jankae/BigRedStopwatch/Pictures/IMG_2714.JPG

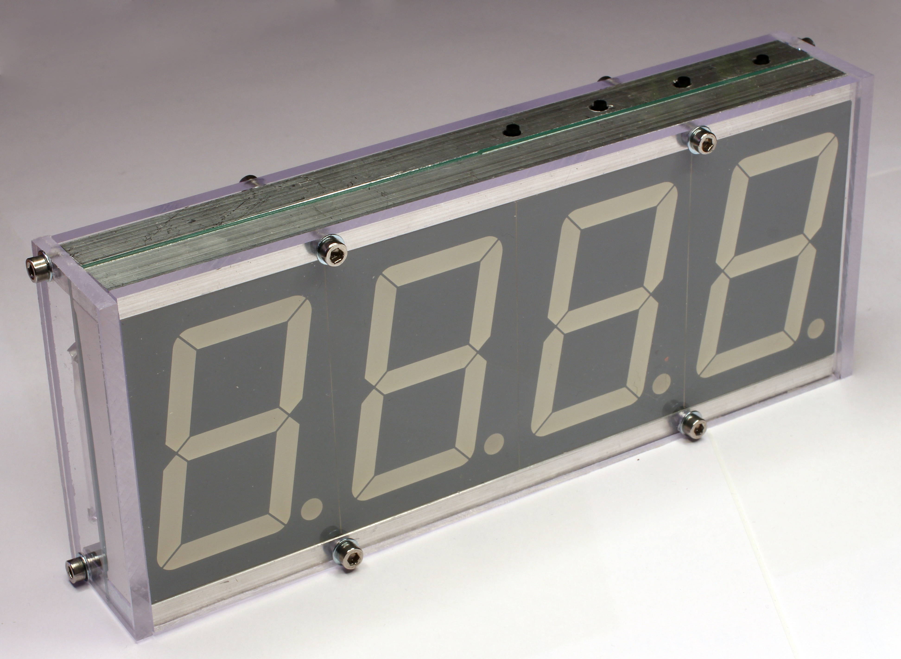
Pictures/IMG_2714.JPG
