jankae/BigRedStopwatch/Pictures/IMG_2717.JPG

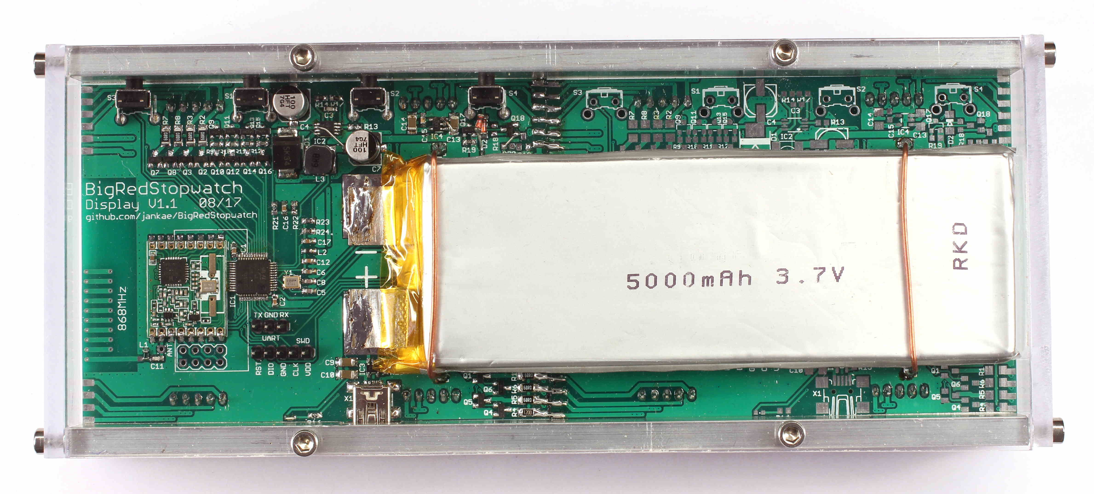
Pictures/IMG_2717.JPG
