jankae/BigRedStopwatch/Pictures/IMG_2719.JPG

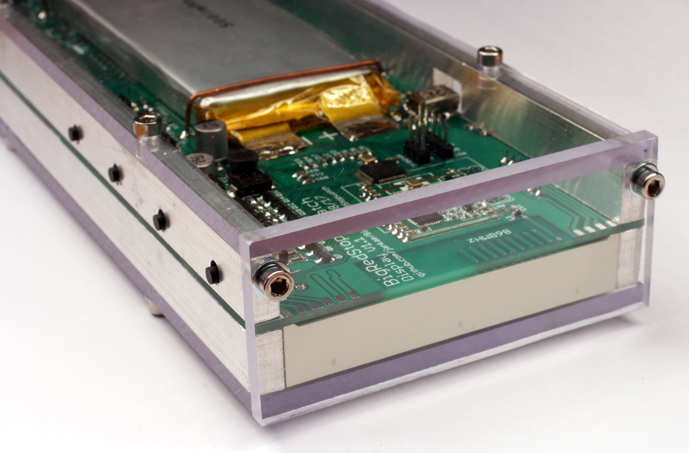
Pictures/IMG_2719.JPG
