jankae/BigRedStopwatch/Pictures/IMG_5150.JPG

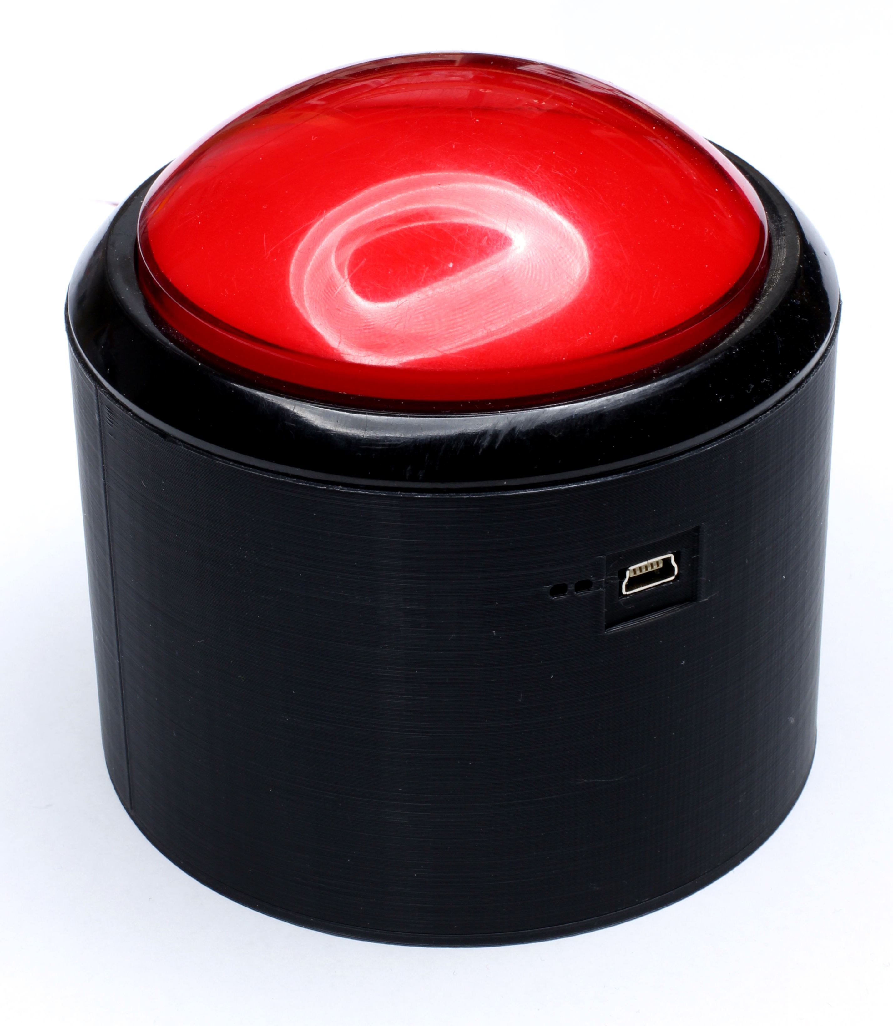
Pictures/IMG_5150.JPG
