jankae/BigRedStopwatch/Pictures/IMG_5152.JPG

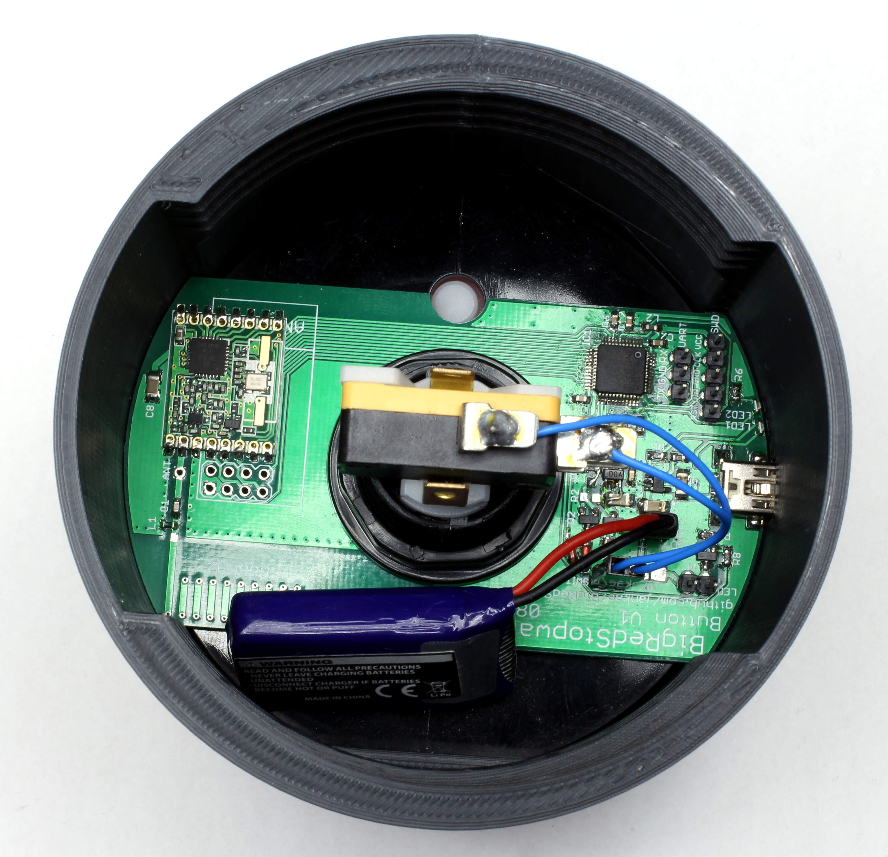
Pictures/IMG_5152.JPG
