jankae/BigRedStopwatch/Pictures/IMG_5153.JPG

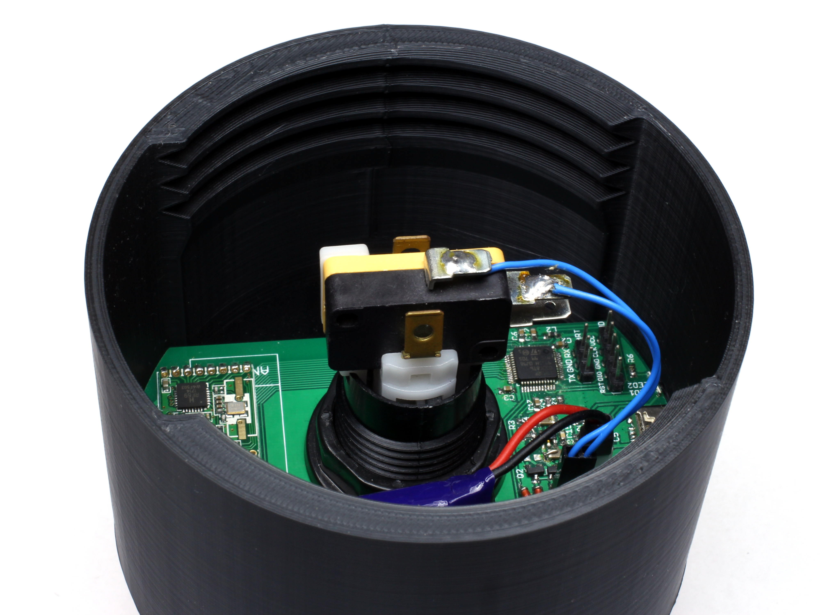
Pictures/IMG_5153.JPG
